lmayencourt/wordclock/3d printed/stencil_holder_v2.stl

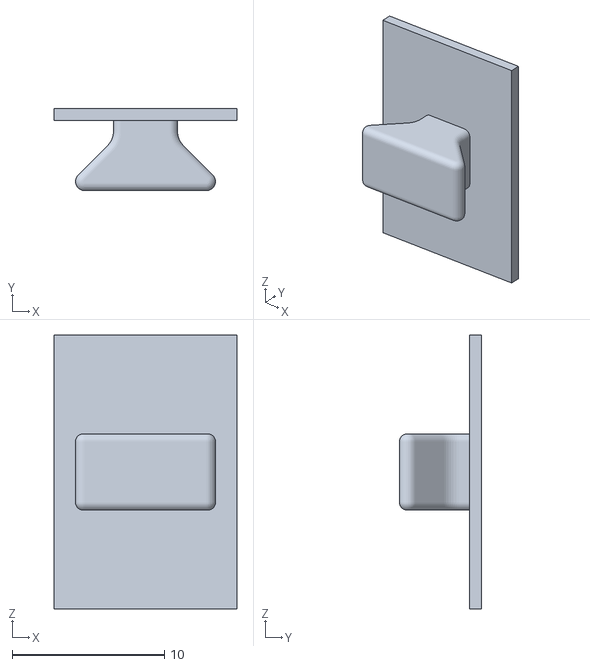
[picture p15: CAD file, 2021-05-20]
3d printed/stencil_holder_v2.stl
12.0 x 5.40 x 18.0
