lmayencourt/wordclock/crates/cross_compiled/src/persistent_settings.rs

/* SPDX-License-Identifier: MIT
 *
 * This files uses part of code from:
 * https://github.com/taunusflieger/anemometer/blob/master/anemometer-production/src/configuration.rs
 * Copyright (c) 2021-2023 Michael Zill
 *
 * Copyright (c) 2023 Louis Mayencourt
 */

use anyhow::{Result, Context};

use esp_idf_svc::nvs::*;
use esp_idf_sys::*;

use application::configuration::*;

const NVS_STRING_READ_BUFFER_SIZE: usize = 180;

pub struct NonVolatileStorage;

impl PersistentStorage for NonVolatileStorage {
    fn load_string(&mut self, key: &str) -> Result<String> {
        let memory_partition = EspCustomNvsPartition::take("nvs").context("Partition `nvs`doesn't exist")?;
        let nvs = EspCustomNvs::new(memory_partition.clone(), "wifi_config", false).context("Partition `nvs` doesn't have a `wifi_config` namespace")?;

        Ok(get_string_from_nvs(&nvs, key)?)
    }

    fn store_string(&mut self, key: &str, value: &str) -> Result<()> {
        let memory_partition = EspCustomNvsPartition::take("nvs").context("Partition `nvs`doesn't exist")?;
        let mut nvs = EspCustomNvs::new(memory_partition.clone(), "wifi_config", true).context("Partition `nvs` doesn't have a `wifi_config` namespace")?;

        nvs.set_str(key, value)?;
        Ok(())
    }
}

fn get_string_from_nvs(nvs: &EspCustomNvs, key: &str) -> Result<String, EspError> {
    let mut nvm_str_buffer: [u8; NVS_STRING_READ_BUFFER_SIZE] = [0; NVS_STRING_READ_BUFFER_SIZE];
    nvs.get_str(key, &mut nvm_str_buffer)?;

    // remove any tailing zeros
    Ok(String::from(
        core::str::from_utf8(
            &(nvm_str_buffer[0..nvm_str_buffer.iter().position(|&x| x == 0).unwrap()]),
        )
        .unwrap(),
    ))
}

use core::ptr;
use std::ffi::CString;
use esp_idf_svc::handle::RawHandle;

pub trait EspNvsExtention {
    fn length_str(&self, name: &str) -> Result<Option<usize>, EspError>;
    fn get_str<'a>(&self, name: &str, buf: &'a mut [u8]) -> Result<Option<&'a [u8]>, EspError>;
    fn set_str(&mut self, name: &str, val: &str) -> Result<bool, EspError>;
}

impl EspNvsExtention for EspCustomNvs {
    fn length_str(&self, name: &str) -> Result<Option<usize>, EspError> {
        let c_key = CString::new(name).unwrap();

        #[allow(unused_assignments)]
        let mut len = 0;

        match unsafe {
            nvs_get_str(
                self.handle(),
                c_key.as_ptr(),
                ptr::null_mut(),
                &mut len as *mut _,
            )
        } {
            ESP_ERR_NVS_NOT_FOUND => Ok(None),
            err => {
                // bail on error
                esp!(err)?;

                Ok(Some(len))
            }
        }
    }

    fn get_str<'a>(&self, name: &str, buf: &'a mut [u8]) -> Result<Option<&'a [u8]>, EspError> {
        let c_key = CString::new(name).unwrap();

        #[allow(unused_assignments)]
        let mut len = 0;
        match unsafe {
            len = buf.len();
            nvs_get_str(
                self.handle(),
                c_key.as_ptr(),
                buf.as_mut_ptr() as *mut _,
                &mut len as *mut _,
            )
        } {
            ESP_ERR_NVS_NOT_FOUND => Ok(None),
            err => {
                // bail on error
                esp!(err)?;

                Ok(Some(buf))
            }
        }
    }

    fn set_str(&mut self, name: &str, val: &str) -> Result<bool, EspError> {
        let c_key = CString::new(name).unwrap();
        let c_val = CString::new(val).unwrap();

        // start by just clearing this key
        unsafe { nvs_erase_key(self.handle(), c_key.as_ptr()) };

        esp!(unsafe { nvs_set_str(self.handle(), c_key.as_ptr(), c_val.as_ptr(),) })?;

        esp!(unsafe { nvs_commit(self.handle()) })?;

        Ok(true)
    }
}
