lmayencourt/wordclock/crates/cross_compiled/src/lib.rs

/* SPDX-License-Identifier: MIT
 * Copyright (c) 2023 Louis Mayencourt
 */

pub mod esp32_soc;
pub mod ds3231_board_rtc;
pub mod ota_update;
pub mod led_driver;
pub mod http_server;
pub mod network;
pub mod network_time;
pub mod persistent_settings;
pub mod rgb_led_strip_matrix;
